YingK8/ESP32-BLE-Macro-Pad/macro-pad/src/departure_mono_upper_28.c

/*******************************************************************************
 * Size: 28 px
 * Bpp: 1
 * Opts: --bpp 1 --size 28 --stride 1 --align 1 --font DepartureMono-Regular.woff --symbols 1234567890:QWERTYUIOP[]\{}|ASDFGHJKL;':"ZXCVBNM,./>?<!@#$%^&*()_+-=  --format lvgl -o departure_mono_upper_28.c
 ******************************************************************************/

#ifdef __has_include
    #if __has_include("lvgl.h")
        #ifndef LV_LVGL_H_INCLUDE_SIMPLE
            #define LV_LVGL_H_INCLUDE_SIMPLE
        #endif
    #endif
#endif

#ifdef LV_LVGL_H_INCLUDE_SIMPLE
    #include "lvgl.h"
#else
    #include "lvgl/lvgl.h"
#endif



#ifndef DEPARTURE_MONO_UPPER_28
#define DEPARTURE_MONO_UPPER_28 1
#endif

#if DEPARTURE_MONO_UPPER_28

/*-----------------
 *    BITMAPS
 *----------------*/

/*Store the image of the glyphs*/
static LV_ATTRIBUTE_LARGE_CONST const uint8_t glyph_bitmap[] = {
    /* U+0020 " " */
    0x0,

    /* U+0021 "!" */
    0xff, 0xff, 0xff, 0xff, 0xff, 0xf8, 0x3, 0xf0,

    /* U+0022 "\"" */
    0xe7, 0xe7, 0xe7, 0xe7, 0xe7, 0xe7, 0xe7,

    /* U+0023 "#" */
    0x0, 0xc3, 0x0, 0x30, 0xc0, 0xc, 0x30, 0x3,
    0xc, 0x0, 0xc3, 0xf, 0xff, 0xf3, 0xff, 0xfc,
    0x1c, 0xf0, 0x7, 0x3c, 0x1, 0xcf, 0x0, 0x73,
    0xc0, 0x1c, 0xf0, 0x7, 0x3c, 0x3f, 0xff, 0xcf,
    0xff, 0xf0, 0xe3, 0x0, 0x38, 0xc0, 0xe, 0x30,
    0x3, 0x8c, 0x0, 0xe3, 0x0,

    /* U+0024 "$" */
    0x7, 0x0, 0x38, 0x1, 0xc0, 0x3f, 0x81, 0xfc,
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
    0x3, 0x80, 0x1c, 0x0, 0xe0, 0x7, 0x0, 0x0,
    0x0, 0x3e, 0x1, 0xf0, 0x70, 0x3, 0x80, 0x1c,
    0x0, 0xe0, 0x7, 0x0, 0x38, 0x1, 0xc0, 0xe,
    0x0, 0x70, 0x3, 0x83, 0xe0, 0x1f, 0x0
};


/*---------------------
 *  GLYPH DESCRIPTION
 *--------------------*/

static const lv_font_fmt_txt_glyph_dsc_t glyph_dsc[] = {
    {.bitmap_index = 0, .adv_w = 0, .box_w = 0, .box_h = 0, .ofs_x = 0, .ofs_y = 0} /* id = 0 reserved */,
    {.bitmap_index = 0, .adv_w = 285, .box_w = 1, .box_h = 1, .ofs_x = 0, .ofs_y = 0},
    {.bitmap_index = 1, .adv_w = 285, .box_w = 3, .box_h = 20, .ofs_x = 8, .ofs_y = 0},
    {.bitmap_index = 9, .adv_w = 285, .box_w = 8, .box_h = 7, .ofs_x = 5, .ofs_y = 13},
    {.bitmap_index = 16, .adv_w = 285, .box_w = 18, .box_h = 20, .ofs_x = 0, .ofs_y = 0},
    {.bitmap_index = 61, .adv_w = 285, .box_w = 13, .box_h = 25, .ofs_x = 3, .ofs_y = -2},
    {.bitmap_index = 102, .adv_w = 285, .box_w = 15, .box_h = 20, .ofs_x = 3, .ofs_y = 0},
    {.bitmap_index = 140, .adv_w = 285, .box_w = 15, .box_h = 20, .ofs_x = 3, .ofs_y = 0},
    {.bitmap_index = 178, .adv_w = 285, .box_w = 3, .box_h = 7, .ofs_x = 8, .ofs_y = 13},
    {.bitmap_index = 181, .adv_w = 285, .box_w = 9, .box_h = 24, .ofs_x = 5, .ofs_y = -2},
    {.bitmap_index = 208, .adv_w = 285, .box_w = 9, .box_h = 24, .ofs_x = 5, .ofs_y = -2},
    {.bitmap_index = 235, .adv_w = 285, .box_w = 13, .box_h = 12, .ofs_x = 3, .ofs_y = 8},
    {.bitmap_index = 255, .adv_w = 285, .box_w = 13, .box_h = 12, .ofs_x = 3, .ofs_y = 3},
    {.bitmap_index = 275, .adv_w = 285, .box_w = 5, .box_h = 7, .ofs_x = 5, .ofs_y = -2},
    {.bitmap_index = 280, .adv_w = 285, .box_w = 8, .box_h = 2, .ofs_x = 5, .ofs_y = 8},
    {.bitmap_index = 282, .adv_w = 285, .box_w = 3, .box_h = 5, .ofs_x = 8, .ofs_y = 0},
    {.bitmap_index = 284, .adv_w = 285, .box_w = 13, .box_h = 25, .ofs_x = 3, .ofs_y = -2},
    {.bitmap_index = 325, .adv_w = 285, .box_w = 13, .box_h = 20, .ofs_x = 3, .ofs_y = 0},
    {.bitmap_index = 358, .adv_w = 285, .box_w = 13, .box_h = 20, .ofs_x = 3, .ofs_y = 0},
    {.bitmap_index = 391, .adv_w = 285, .box_w = 13, .box_h = 20, .ofs_x = 3, .ofs_y = 0},
    {.bitmap_index = 424, .adv_w = 285, .box_w = 13, .box_h = 20, .ofs_x = 3, .ofs_y = 0},
    {.bitmap_index = 457, .adv_w = 285, .box_w = 13, .box_h = 20, .ofs_x = 3, .ofs_y = 0},
    {.bitmap_index = 490, .adv_w = 285, .box_w = 13, .box_h = 20, .ofs_x = 3, .ofs_y = 0},
    {.bitmap_index = 523, .adv_w = 285, .box_w = 13, .box_h = 20, .ofs_x = 3, .ofs_y = 0},
    {.bitmap_index = 556, .adv_w = 285, .box_w = 13, .box_h = 20, .ofs_x = 2, .ofs_y = 0},
    {.bitmap_index = 589, .adv_w = 285, .box_w = 13, .box_h = 20, .ofs_x = 3, .ofs_y = 0},
    {.bitmap_index = 622, .adv_w = 285, .box_w = 13, .box_h = 20, .ofs_x = 3, .ofs_y = 0},
    {.bitmap_index = 655, .adv_w = 285, .box_w = 3, .box_h = 15, .ofs_x = 8, .ofs_y = 0},
    {.bitmap_index = 661, .adv_w = 285, .box_w = 5, .box_h = 17, .ofs_x = 5, .ofs_y = -2},
    {.bitmap_index = 672, .adv_w = 285, .box_w = 10, .box_h = 17, .ofs_x = 3, .ofs_y = 0},
    {.bitmap_index = 694, .adv_w = 285, .box_w = 13, .box_h = 7, .ofs_x = 3, .ofs_y = 5},
    {.bitmap_index = 706, .adv_w = 285, .box_w = 10, .box_h = 17, .ofs_x = 5, .ofs_y = 0},
    {.bitmap_index = 728, .adv_w = 285, .box_w = 13, .box_h = 20, .ofs_x = 3, .ofs_y = 0},
    {.bitmap_index = 761, .adv_w = 285, .box_w = 13, .box_h = 20, .ofs_x = 3, .ofs_y = 0},
    {.bitmap_index = 794, .adv_w = 285, .box_w = 13, .box_h = 20, .ofs_x = 3, .ofs_y = 0},
    {.bitmap_index = 827, .adv_w = 285, .box_w = 13, .box_h = 20, .ofs_x = 3, .ofs_y = 0},
    {.bitmap_index = 860, .adv_w = 285, .box_w = 13, .box_h = 20, .ofs_x = 3, .ofs_y = 0},
    {.bitmap_index = 893, .adv_w = 285, .box_w = 13, .box_h = 20, .ofs_x = 3, .ofs_y = 0},
    {.bitmap_index = 926, .adv_w = 285, .box_w = 13, .box_h = 20, .ofs_x = 3, .ofs_y = 0},
    {.bitmap_index = 959, .adv_w = 285, .box_w = 13, .box_h = 20, .ofs_x = 3, .ofs_y = 0},
    {.bitmap_index = 992, .adv_w = 285, .box_w = 13, .box_h = 20, .ofs_x = 3, .ofs_y = 0},
    {.bitmap_index = 1025, .adv_w = 285, .box_w = 13, .box_h = 20, .ofs_x = 3, .ofs_y = 0},
    {.bitmap_index = 1058, .adv_w = 285, .box_w = 13, .box_h = 20, .ofs_x = 3, .ofs_y = 0},
    {.bitmap_index = 1091, .adv_w = 285, .box_w = 13, .box_h = 20, .ofs_x = 3, .ofs_y = 0},
    {.bitmap_index = 1124, .adv_w = 285, .box_w = 13, .box_h = 20, .ofs_x = 3, .ofs_y = 0},
    {.bitmap_index = 1157, .adv_w = 285, .box_w = 13, .box_h = 20, .ofs_x = 3, .ofs_y = 0},
    {.bitmap_index = 1190, .adv_w = 285, .box_w = 13, .box_h = 20, .ofs_x = 3, .ofs_y = 0},
    {.bitmap_index = 1223, .adv_w = 285, .box_w = 13, .box_h = 20, .ofs_x = 3, .ofs_y = 0},
    {.bitmap_index = 1256, .adv_w = 285, .box_w = 13, .box_h = 20, .ofs_x = 3, .ofs_y = 0},
    {.bitmap_index = 1289, .adv_w = 285, .box_w = 13, .box_h = 20, .ofs_x = 3, .ofs_y = 0},
    {.bitmap_index = 1322, .adv_w = 285, .box_w = 13, .box_h = 22, .ofs_x = 3, .ofs_y = -2},
    {.bitmap_index = 1358, .adv_w = 285, .box_w = 13, .box_h = 20, .ofs_x = 3, .ofs_y = 0},
    {.bitmap_index = 1391, .adv_w = 285, .box_w = 13, .box_h = 20, .ofs_x = 3, .ofs_y = 0},
    {.bitmap_index = 1424, .adv_w = 285, .box_w = 13, .box_h = 20, .ofs_x = 3, .ofs_y = 0},
    {.bitmap_index = 1457, .adv_w = 285, .box_w = 13, .box_h = 20, .ofs_x = 3, .ofs_y = 0},
    {.bitmap_index = 1490, .adv_w = 285, .box_w = 13, .box_h = 20, .ofs_x = 3, .ofs_y = 0},
    {.bitmap_index = 1523, .adv_w = 285, .box_w = 13, .box_h = 20, .ofs_x = 3, .ofs_y = 0},
    {.bitmap_index = 1556, .adv_w = 285, .box_w = 13, .box_h = 20, .ofs_x = 3, .ofs_y = 0},
    {.bitmap_index = 1589, .adv_w = 285, .box_w = 13, .box_h = 20, .ofs_x = 3, .ofs_y = 0},
    {.bitmap_index = 1622, .adv_w = 285, .box_w = 13, .box_h = 20, .ofs_x = 3, .ofs_y = 0},
    {.bitmap_index = 1655, .adv_w = 285, .box_w = 8, .box_h = 25, .ofs_x = 5, .ofs_y = -2},
    {.bitmap_index = 1680, .adv_w = 285, .box_w = 13, .box_h = 25, .ofs_x = 3, .ofs_y = -2},
    {.bitmap_index = 1721, .adv_w = 285, .box_w = 8, .box_h = 25, .ofs_x = 5, .ofs_y = -2},
    {.bitmap_index = 1746, .adv_w = 285, .box_w = 9, .box_h = 5, .ofs_x = 5, .ofs_y = 15},
    {.bitmap_index = 1752, .adv_w = 285, .box_w = 13, .box_h = 2, .ofs_x = 3, .ofs_y = 0},
    {.bitmap_index = 1756, .adv_w = 285, .box_w = 13, .box_h = 24, .ofs_x = 0, .ofs_y = -2},
    {.bitmap_index = 1795, .adv_w = 285, .box_w = 3, .box_h = 25, .ofs_x = 8, .ofs_y = -2},
    {.bitmap_index = 1805, .adv_w = 285, .box_w = 13, .box_h = 24, .ofs_x = 5, .ofs_y = -2}
};

/*---------------------
 *  CHARACTER MAPPING
 *--------------------*/



/*Collect the unicode lists and glyph_id offsets*/
static const lv_font_fmt_txt_cmap_t cmaps[] =
{
    {
        .range_start = 32, .range_length = 64, .glyph_id_start = 1,
        .unicode_list = NULL, .glyph_id_ofs_list = NULL, .list_length = 0, .type = LV_FONT_FMT_TXT_CMAP_FORMAT0_TINY
    },
    {
        .range_start = 123, .range_length = 3, .glyph_id_start = 65,
        .unicode_list = NULL, .glyph_id_ofs_list = NULL, .list_length = 0, .type = LV_FONT_FMT_TXT_CMAP_FORMAT0_TINY
    }
};



/*--------------------
 *  ALL CUSTOM DATA
 *--------------------*/

#if LVGL_VERSION_MAJOR == 8
/*Store all the custom data of the font*/
static  lv_font_fmt_txt_glyph_cache_t cache;
#endif

#if LVGL_VERSION_MAJOR >= 8
static const lv_font_fmt_txt_dsc_t font_dsc = {
#else
static lv_font_fmt_txt_dsc_t font_dsc = {
#endif
    .glyph_bitmap = glyph_bitmap,
    .glyph_dsc = glyph_dsc,
    .cmaps = cmaps,
    .kern_dsc = NULL,
    .kern_scale = 0,
    .cmap_num = 2,
    .bpp = 1,
    .kern_classes = 0,
    .bitmap_format = 0,
#if LVGL_VERSION_MAJOR == 8
    .cache = &cache
#endif

};



/*-----------------
 *  PUBLIC FONT
 *----------------*/

/*Initialize a public general font descriptor*/
#if LVGL_VERSION_MAJOR >= 8
const lv_font_t departure_mono_upper_28 = {
#else
lv_font_t departure_mono_upper_28 = {
#endif
    .get_glyph_dsc = lv_font_get_glyph_dsc_fmt_txt,    /*Function pointer to get glyph's data*/
    .get_glyph_bitmap = lv_font_get_bitmap_fmt_txt,    /*Function pointer to get glyph's bitmap*/
    .line_height = 25,          /*The maximum line height required by the font*/
    .base_line = 2,             /*Baseline measured from the bottom of the line*/
#if !(LVGL_VERSION_MAJOR == 6 && LVGL_VERSION_MINOR == 0)
    .subpx = LV_FONT_SUBPX_NONE,
#endif
#if LV_VERSION_CHECK(7, 4, 0) || LVGL_VERSION_MAJOR >= 8
    .underline_position = -3,
    .underline_thickness = 2,
#endif
    .dsc = &font_dsc,          /*The custom font data. Will be accessed by `get_glyph_bitmap/dsc` */
#if LV_VERSION_CHECK(8, 2, 0) || LVGL_VERSION_MAJOR >= 9
    .fallback = NULL,
#endif
    .user_data = NULL,
};



#endif /*#if DEPARTURE_MONO_UPPER_28*/
