YingK8/ESP32-BLE-Macro-Pad/macro-pad/src/departure_mono_upper_40.c

/*******************************************************************************
 * Size: 40 px
 * Bpp: 1
 * Opts: --bpp 1 --size 40 --no-compress --stride 1 --align 1 --font
 *DepartureMono-Regular.woff --symbols
 *1234567890:qwertyuiop[]\{}|asdfghjkl;':"zxcvbnm,./>?<!@#$%^&*()_+-=  --format
 *lvgl -o departure_mono_upper_40.c
 ******************************************************************************/

#ifdef __has_include
#if __has_include("lvgl.h")
#ifndef LV_LVGL_H_INCLUDE_SIMPLE
#define LV_LVGL_H_INCLUDE_SIMPLE
#endif
#endif
#endif

#ifdef LV_LVGL_H_INCLUDE_SIMPLE
#include "lvgl.h"
#else
#include "lvgl/lvgl.h"
#endif

#ifndef DEPARTURE_MONO_UPPER_40
#define DEPARTURE_MONO_UPPER_40 1
#endif

#if DEPARTURE_MONO_UPPER_40

/*-----------------
 *    BITMAPS
 *----------------*/

/*Store the image of the glyphs*/
static LV_ATTRIBUTE_LARGE_CONST const uint8_t glyph_bitmap[] = {
    /* U+0020 " " */
    0x0,

    /* U+0021 "!" */
    0xff, 0xff, 0xff, 0xff, 0xff, 0xff, 0xff, 0xff, 0xff, 0xff, 0xff, 0x0, 0x0,
    0xff, 0xf0,

    /* U+0022 "\"" */
    0xf1, 0xfe, 0x3f, 0xc7, 0xf8, 0xff, 0x1f, 0xe3, 0xfc, 0x7f, 0x8f, 0xf1,
    0xfe, 0x3f, 0xc7, 0x80,

    /* U+0023 "#" */
    0x0, 0x1e, 0x1e, 0x0, 0x7, 0x87, 0x80, 0x1, 0xe1, 0xe0, 0x0, 0x78, 0x78,
    0x0, 0x1e, 0x1e, 0x0, 0x7, 0x87, 0x80, 0x1, 0xe1, 0xe0, 0x7f, 0xff, 0xff,
    0x1f, 0xff, 0xff, 0xc7, 0xff, 0xff, 0xf1, 0xff, 0xff, 0xfc, 0x7, 0x87, 0x80,
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
     .adv_w = 407,
     .box_w = 4,
     .box_h = 36,
     .ofs_x = 11,
     .ofs_y = -4},
    {.bitmap_index = 3431,
     .adv_w = 407,
     .box_w = 18,
     .box_h = 36,
     .ofs_x = 7,
     .ofs_y = -3}};

/*---------------------
 *  CHARACTER MAPPING
 *--------------------*/

/*Collect the unicode lists and glyph_id offsets*/
static const lv_font_fmt_txt_cmap_t cmaps[] = {
    {.range_start = 32,
     .range_length = 33,
     .glyph_id_start = 1,
     .unicode_list = NULL,
     .glyph_id_ofs_list = NULL,
     .list_length = 0,
     .type = LV_FONT_FMT_TXT_CMAP_FORMAT0_TINY},
    {.range_start = 91,
     .range_length = 5,
     .glyph_id_start = 34,
     .unicode_list = NULL,
     .glyph_id_ofs_list = NULL,
     .list_length = 0,
     .type = LV_FONT_FMT_TXT_CMAP_FORMAT0_TINY},
    {.range_start = 97,
     .range_length = 29,
     .glyph_id_start = 39,
     .unicode_list = NULL,
     .glyph_id_ofs_list = NULL,
     .list_length = 0,
     .type = LV_FONT_FMT_TXT_CMAP_FORMAT0_TINY}};

/*--------------------
 *  ALL CUSTOM DATA
 *--------------------*/

#if LVGL_VERSION_MAJOR == 8
/*Store all the custom data of the font*/
static lv_font_fmt_txt_glyph_cache_t cache;
#endif

#if LVGL_VERSION_MAJOR >= 8
static const lv_font_fmt_txt_dsc_t font_dsc = {
#else
static lv_font_fmt_txt_dsc_t font_dsc = {
#endif
    .glyph_bitmap = glyph_bitmap,
    .glyph_dsc = glyph_dsc,
    .cmaps = cmaps,
    .kern_dsc = NULL,
    .kern_scale = 0,
    .cmap_num = 3,
    .bpp = 1,
    .kern_classes = 0,
    .bitmap_format = 0,
#if LVGL_VERSION_MAJOR == 8
    .cache = &cache
#endif

};

/*-----------------
 *  PUBLIC FONT
 *----------------*/

/*Initialize a public general font descriptor*/
#if LVGL_VERSION_MAJOR >= 8
const lv_font_t departure_mono_upper_40 = {
#else
lv_font_t departure_mono_upper_40 = {
#endif
    .get_glyph_dsc =
        lv_font_get_glyph_dsc_fmt_txt, /*Function pointer to get glyph's data*/
    .get_glyph_bitmap =
        lv_font_get_bitmap_fmt_txt, /*Function pointer to get glyph's bitmap*/
    .line_height = 40, /*The maximum line height required by the font*/
    .base_line = 7,    /*Baseline measured from the bottom of the line*/
#if !(LVGL_VERSION_MAJOR == 6 && LVGL_VERSION_MINOR == 0)
    .subpx = LV_FONT_SUBPX_NONE,
#endif
#if LV_VERSION_CHECK(7, 4, 0) || LVGL_VERSION_MAJOR >= 8
    .underline_position = -4,
    .underline_thickness = 2,
#endif

    .dsc = &font_dsc, /*The custom font data. Will be accessed by
                         `get_glyph_bitmap/dsc` */
#if LV_VERSION_CHECK(8, 2, 0) || LVGL_VERSION_MAJOR >= 9
    .fallback = NULL,
#endif
    .user_data = NULL,
};

#endif /*#if DEPARTURE_MONO_UPPER_40*/
