YingK8/ESP32-BLE-Macro-Pad/macro-pad/src/monogram_lower_40.c

/*******************************************************************************
 * Size: 40 px
 * Bpp: 1
 * Opts: --bpp 1 --size 40 --stride 1 --align 1 --font monogram-extended.ttf --symbols 1234567890:qwertyuiop[]\{}|asdfghjkl;':"zxcvbnm,./>?<!@#$%^&*()_+-=  --format lvgl -o monogram_lower_40.c
 ******************************************************************************/

#ifdef __has_include
    #if __has_include("lvgl.h")
        #ifndef LV_LVGL_H_INCLUDE_SIMPLE
            #define LV_LVGL_H_INCLUDE_SIMPLE
        #endif
    #endif
#endif

#ifdef LV_LVGL_H_INCLUDE_SIMPLE
    #include "lvgl.h"
#else
    #include "lvgl/lvgl.h"
#endif



#ifndef MONOGRAM_LOWER_40
#define MONOGRAM_LOWER_40 1
#endif

#if MONOGRAM_LOWER_40

/*-----------------
 *    BITMAPS
 *----------------*/

/*Store the image of the glyphs*/
static LV_ATTRIBUTE_LARGE_CONST const uint8_t glyph_bitmap[] = {
    /* U+0020 " " */
    0x0,

    /* U+0021 "!" */
    0xff, 0xff, 0xff, 0xff, 0xfe, 0x0, 0xfc,

    /* U+0022 "\"" */
    0xe7, 0xe7, 0xe7, 0xe7, 0xe7, 0xe7, 0xe7, 0xe7,

    /* U+0023 "#" */
    0x39, 0xc1, 0xce, 0x3f, 0xff, 0xff, 0xf3, 0x9c,
    0x1c, 0xe0, 0xe7, 0x7, 0x38, 0x39, 0xc1, 0xce,
    0x3f, 0xff, 0xff, 0xf3, 0x9c, 0x1c, 0xe0, 0xe7,
    0x0,

    /* U+0024 "$" */
    0x7, 0x0, 0x38, 0x1, 0xc0, 0x3f, 0xf1, 0xff,
    0xf3, 0x83, 0x9c, 0x4, 0xe0, 0x1f, 0xc0, 0xfe,
    0x1, 0xce, 0xe, 0x70, 0x70, 0x7f, 0xe3, 0xff,
    0x0, 0xe0, 0x7, 0x0, 0x38, 0x0,

    /* U+0025 "%" */
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

    /* U+007C "|" */
    0xff, 0xff, 0xff, 0xff, 0xff, 0xff, 0xfc,

    /* U+007D "}" */
    0xe0, 0x70, 0x6, 0x3, 0x1, 0x80, 0xc0, 0x60,
    0x0, 0x3, 0x81, 0xc6, 0x3, 0x1, 0x80, 0xc0,
    0x60, 0x0, 0xe0, 0x70, 0x0
};


/*---------------------
 *  GLYPH DESCRIPTION
 *--------------------*/

static const lv_font_fmt_txt_glyph_dsc_t glyph_dsc[] = {
    {.bitmap_index = 0, .adv_w = 0, .box_w = 0, .box_h = 0, .ofs_x = 0, .ofs_y = 0} /* id = 0 reserved */,
    {.bitmap_index = 0, .adv_w = 240, .box_w = 1, .box_h = 1, .ofs_x = 0, .ofs_y = 0},
    {.bitmap_index = 1, .adv_w = 240, .box_w = 3, .box_h = 18, .ofs_x = 5, .ofs_y = 0},
    {.bitmap_index = 8, .adv_w = 240, .box_w = 8, .box_h = 8, .ofs_x = 2, .ofs_y = 10},
    {.bitmap_index = 16, .adv_w = 240, .box_w = 13, .box_h = 15, .ofs_x = 0, .ofs_y = 0},
    {.bitmap_index = 41, .adv_w = 240, .box_w = 13, .box_h = 18, .ofs_x = 0, .ofs_y = 0},
    {.bitmap_index = 71, .adv_w = 240, .box_w = 13, .box_h = 18, .ofs_x = 0, .ofs_y = 0},
    {.bitmap_index = 101, .adv_w = 240, .box_w = 13, .box_h = 18, .ofs_x = 0, .ofs_y = 0},
    {.bitmap_index = 131, .adv_w = 240, .box_w = 3, .box_h = 8, .ofs_x = 5, .ofs_y = 10},
    {.bitmap_index = 134, .adv_w = 240, .box_w = 5, .box_h = 18, .ofs_x = 5, .ofs_y = 0},
    {.bitmap_index = 146, .adv_w = 240, .box_w = 5, .box_h = 18, .ofs_x = 2, .ofs_y = 0},
    {.bitmap_index = 158, .adv_w = 240, .box_w = 13, .box_h = 13, .ofs_x = 0, .ofs_y = 3},
    {.bitmap_index = 180, .adv_w = 240, .box_w = 13, .box_h = 13, .ofs_x = 0, .ofs_y = 3},
    {.bitmap_index = 202, .adv_w = 240, .box_w = 5, .box_h = 7, .ofs_x = 2, .ofs_y = -2},
    {.bitmap_index = 207, .adv_w = 240, .box_w = 13, .box_h = 2, .ofs_x = 0, .ofs_y = 8},
    {.bitmap_index = 211, .adv_w = 240, .box_w = 3, .box_h = 5, .ofs_x = 5, .ofs_y = 0},
    {.bitmap_index = 213, .adv_w = 240, .box_w = 13, .box_h = 18, .ofs_x = 0, .ofs_y = 0},
    {.bitmap_index = 243, .adv_w = 240, .box_w = 13, .box_h = 18, .ofs_x = 0, .ofs_y = 0},
    {.bitmap_index = 273, .adv_w = 240, .box_w = 13, .box_h = 18, .ofs_x = 0, .ofs_y = 0},
    {.bitmap_index = 303, .adv_w = 240, .box_w = 13, .box_h = 18, .ofs_x = 0, .ofs_y = 0},
    {.bitmap_index = 333, .adv_w = 240, .box_w = 13, .box_h = 18, .ofs_x = 0, .ofs_y = 0},
    {.bitmap_index = 363, .adv_w = 240, .box_w = 13, .box_h = 18, .ofs_x = 0, .ofs_y = 0},
    {.bitmap_index = 393, .adv_w = 240, .box_w = 13, .box_h = 18, .ofs_x = 0, .ofs_y = 0},
    {.bitmap_index = 423, .adv_w = 240, .box_w = 13, .box_h = 18, .ofs_x = 0, .ofs_y = 0},
    {.bitmap_index = 453, .adv_w = 240, .box_w = 13, .box_h = 18, .ofs_x = 0, .ofs_y = 0},
    {.bitmap_index = 483, .adv_w = 240, .box_w = 13, .box_h = 18, .ofs_x = 0, .ofs_y = 0},
    {.bitmap_index = 513, .adv_w = 240, .box_w = 13, .box_h = 18, .ofs_x = 0, .ofs_y = 0},
    {.bitmap_index = 543, .adv_w = 240, .box_w = 3, .box_h = 16, .ofs_x = 5, .ofs_y = 0},
    {.bitmap_index = 549, .adv_w = 240, .box_w = 5, .box_h = 18, .ofs_x = 2, .ofs_y = -2},
    {.bitmap_index = 561, .adv_w = 240, .box_w = 13, .box_h = 13, .ofs_x = 0, .ofs_y = 3},
    {.bitmap_index = 583, .adv_w = 240, .box_w = 13, .box_h = 7, .ofs_x = 0, .ofs_y = 6},
    {.bitmap_index = 595, .adv_w = 240, .box_w = 13, .box_h = 13, .ofs_x = 0, .ofs_y = 3},
    {.bitmap_index = 617, .adv_w = 240, .box_w = 13, .box_h = 18, .ofs_x = 0, .ofs_y = 0},
    {.bitmap_index = 647, .adv_w = 240, .box_w = 13, .box_h = 18, .ofs_x = 0, .ofs_y = 0},
    {.bitmap_index = 677, .adv_w = 240, .box_w = 5, .box_h = 18, .ofs_x = 5, .ofs_y = 0},
    {.bitmap_index = 689, .adv_w = 240, .box_w = 13, .box_h = 18, .ofs_x = 0, .ofs_y = 0},
    {.bitmap_index = 719, .adv_w = 240, .box_w = 6, .box_h = 18, .ofs_x = 2, .ofs_y = 0},
    {.bitmap_index = 733, .adv_w = 240, .box_w = 13, .box_h = 7, .ofs_x = 0, .ofs_y = 10},
    {.bitmap_index = 745, .adv_w = 240, .box_w = 13, .box_h = 2, .ofs_x = 0, .ofs_y = 0},
    {.bitmap_index = 749, .adv_w = 240, .box_w = 13, .box_h = 13, .ofs_x = 0, .ofs_y = 0},
    {.bitmap_index = 771, .adv_w = 240, .box_w = 13, .box_h = 18, .ofs_x = 0, .ofs_y = 0},
    {.bitmap_index = 801, .adv_w = 240, .box_w = 13, .box_h = 13, .ofs_x = 0, .ofs_y = 0},
    {.bitmap_index = 823, .adv_w = 240, .box_w = 13, .box_h = 18, .ofs_x = 0, .ofs_y = 0},
    {.bitmap_index = 853, .adv_w = 240, .box_w = 13, .box_h = 13, .ofs_x = 0, .ofs_y = 0},
    {.bitmap_index = 875, .adv_w = 240, .box_w = 13, .box_h = 18, .ofs_x = 0, .ofs_y = 0},
    {.bitmap_index = 905, .adv_w = 240, .box_w = 13, .box_h = 18, .ofs_x = 0, .ofs_y = -5},
    {.bitmap_index = 935, .adv_w = 240, .box_w = 13, .box_h = 18, .ofs_x = 0, .ofs_y = 0},
    {.bitmap_index = 965, .adv_w = 240, .box_w = 13, .box_h = 18, .ofs_x = 0, .ofs_y = 0},
    {.bitmap_index = 995, .adv_w = 240, .box_w = 13, .box_h = 23, .ofs_x = 0, .ofs_y = -5},
    {.bitmap_index = 1033, .adv_w = 240, .box_w = 13, .box_h = 18, .ofs_x = 0, .ofs_y = 0},
    {.bitmap_index = 1063, .adv_w = 240, .box_w = 13, .box_h = 18, .ofs_x = 0, .ofs_y = 0},
    {.bitmap_index = 1093, .adv_w = 240, .box_w = 13, .box_h = 13, .ofs_x = 0, .ofs_y = 0},
    {.bitmap_index = 1115, .adv_w = 240, .box_w = 13, .box_h = 13, .ofs_x = 0, .ofs_y = 0},
    {.bitmap_index = 1137, .adv_w = 240, .box_w = 13, .box_h = 13, .ofs_x = 0, .ofs_y = 0},
    {.bitmap_index = 1159, .adv_w = 240, .box_w = 13, .box_h = 18, .ofs_x = 0, .ofs_y = -5},
    {.bitmap_index = 1189, .adv_w = 240, .box_w = 13, .box_h = 18, .ofs_x = 0, .ofs_y = -5},
    {.bitmap_index = 1219, .adv_w = 240, .box_w = 13, .box_h = 13, .ofs_x = 0, .ofs_y = 0},
    {.bitmap_index = 1241, .adv_w = 240, .box_w = 13, .box_h = 13, .ofs_x = 0, .ofs_y = 0},
    {.bitmap_index = 1263, .adv_w = 240, .box_w = 13, .box_h = 18, .ofs_x = 0, .ofs_y = 0},
    {.bitmap_index = 1293, .adv_w = 240, .box_w = 13, .box_h = 13, .ofs_x = 0, .ofs_y = 0},
    {.bitmap_index = 1315, .adv_w = 240, .box_w = 13, .box_h = 13, .ofs_x = 0, .ofs_y = 0},
    {.bitmap_index = 1337, .adv_w = 240, .box_w = 13, .box_h = 13, .ofs_x = 0, .ofs_y = 0},
    {.bitmap_index = 1359, .adv_w = 240, .box_w = 13, .box_h = 13, .ofs_x = 0, .ofs_y = 0},
    {.bitmap_index = 1381, .adv_w = 240, .box_w = 13, .box_h = 18, .ofs_x = 0, .ofs_y = -5},
    {.bitmap_index = 1411, .adv_w = 240, .box_w = 13, .box_h = 13, .ofs_x = 0, .ofs_y = 0},
    {.bitmap_index = 1433, .adv_w = 240, .box_w = 9, .box_h = 18, .ofs_x = 2, .ofs_y = 0},
    {.bitmap_index = 1454, .adv_w = 240, .box_w = 3, .box_h = 18, .ofs_x = 5, .ofs_y = 0},
    {.bitmap_index = 1461, .adv_w = 240, .box_w = 9, .box_h = 18, .ofs_x = 2, .ofs_y = 0}
};

/*---------------------
 *  CHARACTER MAPPING
 *--------------------*/



/*Collect the unicode lists and glyph_id offsets*/
static const lv_font_fmt_txt_cmap_t cmaps[] =
{
    {
        .range_start = 32, .range_length = 33, .glyph_id_start = 1,
        .unicode_list = NULL, .glyph_id_ofs_list = NULL, .list_length = 0, .type = LV_FONT_FMT_TXT_CMAP_FORMAT0_TINY
    },
    {
        .range_start = 91, .range_length = 5, .glyph_id_start = 34,
        .unicode_list = NULL, .glyph_id_ofs_list = NULL, .list_length = 0, .type = LV_FONT_FMT_TXT_CMAP_FORMAT0_TINY
    },
    {
        .range_start = 97, .range_length = 29, .glyph_id_start = 39,
        .unicode_list = NULL, .glyph_id_ofs_list = NULL, .list_length = 0, .type = LV_FONT_FMT_TXT_CMAP_FORMAT0_TINY
    }
};



/*--------------------
 *  ALL CUSTOM DATA
 *--------------------*/

#if LVGL_VERSION_MAJOR == 8
/*Store all the custom data of the font*/
static  lv_font_fmt_txt_glyph_cache_t cache;
#endif

#if LVGL_VERSION_MAJOR >= 8
static const lv_font_fmt_txt_dsc_t font_dsc = {
#else
static lv_font_fmt_txt_dsc_t font_dsc = {
#endif
    .glyph_bitmap = glyph_bitmap,
    .glyph_dsc = glyph_dsc,
    .cmaps = cmaps,
    .kern_dsc = NULL,
    .kern_scale = 0,
    .cmap_num = 3,
    .bpp = 1,
    .kern_classes = 0,
    .bitmap_format = 0,
#if LVGL_VERSION_MAJOR == 8
    .cache = &cache
#endif

};



/*-----------------
 *  PUBLIC FONT
 *----------------*/

/*Initialize a public general font descriptor*/
#if LVGL_VERSION_MAJOR >= 8
const lv_font_t monogram_lower_40 = {
#else
lv_font_t monogram_lower_40 = {
#endif
    .get_glyph_dsc = lv_font_get_glyph_dsc_fmt_txt,    /*Function pointer to get glyph's data*/
    .get_glyph_bitmap = lv_font_get_bitmap_fmt_txt,    /*Function pointer to get glyph's bitmap*/
    .line_height = 23,          /*The maximum line height required by the font*/
    .base_line = 5,             /*Baseline measured from the bottom of the line*/
#if !(LVGL_VERSION_MAJOR == 6 && LVGL_VERSION_MINOR == 0)
    .subpx = LV_FONT_SUBPX_NONE,
#endif
#if LV_VERSION_CHECK(7, 4, 0) || LVGL_VERSION_MAJOR >= 8
    .underline_position = -5,
    .underline_thickness = 2,
#endif
    .dsc = &font_dsc,          /*The custom font data. Will be accessed by `get_glyph_bitmap/dsc` */
#if LV_VERSION_CHECK(8, 2, 0) || LVGL_VERSION_MAJOR >= 9
    .fallback = NULL,
#endif
    .user_data = NULL,
};



#endif /*#if MONOGRAM_LOWER_40*/
