YingK8/ESP32-BLE-Macro-Pad/macro-pad/src/monogram_lower_counter_125.c

/*******************************************************************************
 * Size: 125 px
 * Bpp: 1
 * Opts: --bpp 1 --size 125 --no-compress --stride 1 --align 1 --font monogram-extended.ttf --symbols 1234567890: --format lvgl -o monogram_lower_counter_125.c
 ******************************************************************************/

#ifdef __has_include
    #if __has_include("lvgl.h")
        #ifndef LV_LVGL_H_INCLUDE_SIMPLE
            #define LV_LVGL_H_INCLUDE_SIMPLE
        #endif
    #endif
#endif

#ifdef LV_LVGL_H_INCLUDE_SIMPLE
    #include "lvgl.h"
#else
    #include "lvgl/lvgl.h"
#endif



#ifndef MONOGRAM_LOWER_COUNTER_125
#define MONOGRAM_LOWER_COUNTER_125 1
#endif

#if MONOGRAM_LOWER_COUNTER_125

/*-----------------
 *    BITMAPS
 *----------------*/

/*Store the image of the glyphs*/
static LV_ATTRIBUTE_LARGE_CONST const uint8_t glyph_bitmap[] = {
    /* U+0030 "0" */
    0x0, 0xff, 0xff, 0xfe, 0x0, 0x1, 0xff, 0xff,
    0xfc, 0x0, 0x3, 0xff, 0xff, 0xf8, 0x0, 0x7,
    0xff, 0xff, 0xf0, 0x0, 0xf, 0xff, 0xff, 0xe0,
    0x0, 0x1f, 0xff, 0xff, 0xc0, 0x0, 0x3f, 0xff,
    0xff, 0x80, 0x0, 0x7f, 0xff, 0xff, 0x0, 0xff,
    0x0, 0x0, 0x1, 0xff, 0xfe, 0x0, 0x0, 0x3,
    0xff, 0xfc, 0x0, 0x0, 0x7, 0xff, 0xf8, 0x0,
    0x0, 0xf, 0xff, 0xf0, 0x0, 0x0, 0x1f, 0xff,
    0xe0, 0x0, 0x0, 0x3f, 0xff, 0xc0, 0x0, 0x0,
    0x7f, 0xff, 0x80, 0x0, 0x0, 0xff, 0xff, 0x0,
    0x0, 0xff, 0xff, 0xfe, 0x0, 0x1, 0xff, 0xff,
    0xfc, 0x0, 0x3, 0xff, 0xff, 0xf8, 0x0, 0x7,
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
    0x0, 0x0, 0x0, 0x0, 0x0, 0x0, 0x0, 0x0,
    0x0, 0x0, 0x0, 0x0, 0x0, 0x0, 0x0, 0x0,
    0xff, 0xff, 0xff, 0xff, 0xff, 0xff, 0xff, 0xff,
    0xff, 0xff, 0xff, 0xff, 0xff, 0xff, 0xff
};


/*---------------------
 *  GLYPH DESCRIPTION
 *--------------------*/

static const lv_font_fmt_txt_glyph_dsc_t glyph_dsc[] = {
    {.bitmap_index = 0, .adv_w = 0, .box_w = 0, .box_h = 0, .ofs_x = 0, .ofs_y = 0} /* id = 0 reserved */,
    {.bitmap_index = 0, .adv_w = 750, .box_w = 39, .box_h = 55, .ofs_x = 0, .ofs_y = 0},
    {.bitmap_index = 269, .adv_w = 750, .box_w = 39, .box_h = 55, .ofs_x = 0, .ofs_y = 0},
    {.bitmap_index = 538, .adv_w = 750, .box_w = 39, .box_h = 55, .ofs_x = 0, .ofs_y = 0},
    {.bitmap_index = 807, .adv_w = 750, .box_w = 39, .box_h = 55, .ofs_x = 0, .ofs_y = 0},
    {.bitmap_index = 1076, .adv_w = 750, .box_w = 39, .box_h = 55, .ofs_x = 0, .ofs_y = 0},
    {.bitmap_index = 1345, .adv_w = 750, .box_w = 39, .box_h = 55, .ofs_x = 0, .ofs_y = 0},
    {.bitmap_index = 1614, .adv_w = 750, .box_w = 39, .box_h = 55, .ofs_x = 0, .ofs_y = 0},
    {.bitmap_index = 1883, .adv_w = 750, .box_w = 40, .box_h = 55, .ofs_x = 0, .ofs_y = 0},
    {.bitmap_index = 2158, .adv_w = 750, .box_w = 39, .box_h = 55, .ofs_x = 0, .ofs_y = 0},
    {.bitmap_index = 2427, .adv_w = 750, .box_w = 39, .box_h = 55, .ofs_x = 0, .ofs_y = 0},
    {.bitmap_index = 2696, .adv_w = 750, .box_w = 8, .box_h = 47, .ofs_x = 16, .ofs_y = 0}
};

/*---------------------
 *  CHARACTER MAPPING
 *--------------------*/



/*Collect the unicode lists and glyph_id offsets*/
static const lv_font_fmt_txt_cmap_t cmaps[] =
{
    {
        .range_start = 48, .range_length = 11, .glyph_id_start = 1,
        .unicode_list = NULL, .glyph_id_ofs_list = NULL, .list_length = 0, .type = LV_FONT_FMT_TXT_CMAP_FORMAT0_TINY
    }
};



/*--------------------
 *  ALL CUSTOM DATA
 *--------------------*/

#if LVGL_VERSION_MAJOR == 8
/*Store all the custom data of the font*/
static  lv_font_fmt_txt_glyph_cache_t cache;
#endif

#if LVGL_VERSION_MAJOR >= 8
static const lv_font_fmt_txt_dsc_t font_dsc = {
#else
static lv_font_fmt_txt_dsc_t font_dsc = {
#endif
    .glyph_bitmap = glyph_bitmap,
    .glyph_dsc = glyph_dsc,
    .cmaps = cmaps,
    .kern_dsc = NULL,
    .kern_scale = 0,
    .cmap_num = 1,
    .bpp = 1,
    .kern_classes = 0,
    .bitmap_format = 0,
#if LVGL_VERSION_MAJOR == 8
    .cache = &cache
#endif

};



/*-----------------
 *  PUBLIC FONT
 *----------------*/

/*Initialize a public general font descriptor*/
#if LVGL_VERSION_MAJOR >= 8
const lv_font_t monogram_lower_counter_125 = {
#else
lv_font_t monogram_lower_counter_125 = {
#endif
    .get_glyph_dsc = lv_font_get_glyph_dsc_fmt_txt,    /*Function pointer to get glyph's data*/
    .get_glyph_bitmap = lv_font_get_bitmap_fmt_txt,    /*Function pointer to get glyph's bitmap*/
    .line_height = 55,          /*The maximum line height required by the font*/
    .base_line = 0,             /*Baseline measured from the bottom of the line*/
#if !(LVGL_VERSION_MAJOR == 6 && LVGL_VERSION_MINOR == 0)
    .subpx = LV_FONT_SUBPX_NONE,
#endif
#if LV_VERSION_CHECK(7, 4, 0) || LVGL_VERSION_MAJOR >= 8
    .underline_position = -16,
    .underline_thickness = 6,
#endif
    .dsc = &font_dsc,          /*The custom font data. Will be accessed by `get_glyph_bitmap/dsc` */
#if LV_VERSION_CHECK(8, 2, 0) || LVGL_VERSION_MAJOR >= 9
    .fallback = NULL,
#endif
    .user_data = NULL,
};



#endif /*#if MONOGRAM_LOWER_COUNTER_125*/
