YingK8/ESP32-BLE-Macro-Pad/macro-pad/src/dots_28.c

/*******************************************************************************
 * Size: 28 px
 * Bpp: 1
 * Opts: --bpp 1 --size 28 --stride 1 --align 1 --font LED Dot-Matrix.ttf --symbols QWERTYUIOPASDFGHJKLZXCVBNM0!:.-123456789?%=+  --format lvgl -o dots_28.c
 ******************************************************************************/

#ifdef __has_include
    #if __has_include("lvgl.h")
        #ifndef LV_LVGL_H_INCLUDE_SIMPLE
            #define LV_LVGL_H_INCLUDE_SIMPLE
        #endif
    #endif
#endif

#ifdef LV_LVGL_H_INCLUDE_SIMPLE
    #include "lvgl.h"
#else
    #include "lvgl/lvgl.h"
#endif



#ifndef DOTS_28
#define DOTS_28 1
#endif

#if DOTS_28

/*-----------------
 *    BITMAPS
 *----------------*/

/*Store the image of the glyphs*/
static LV_ATTRIBUTE_LARGE_CONST const uint8_t glyph_bitmap[] = {
    /* U+0020 " " */
    0x0,

    /* U+0021 "!" */
    0xf3, 0xcf, 0x3c, 0xf0, 0xf,

    /* U+0025 "%" */
    0xd8, 0xf, 0x60, 0x30, 0x0, 0x36, 0x3, 0xd8,
    0xc, 0x0, 0x0, 0x6, 0x0, 0x18, 0x0, 0x0,
    0xc, 0x0, 0x30, 0x0, 0x0, 0x18, 0x0, 0x60,
    0x0, 0x0, 0x30, 0x1b, 0xc0, 0x6c, 0x0, 0xc,
    0x6, 0xf0, 0x1b,

    /* U+002B "+" */
    0x0, 0x0, 0xc, 0x0, 0x30, 0x0, 0x80, 0x3,
    0x0, 0xc, 0xc, 0xb4, 0xb6, 0xdf, 0xda, 0x48,
    0xc, 0x0, 0x30, 0x0, 0x80, 0x3, 0x0, 0xc,
    0x0, 0x20, 0x0,

    /* U+002D "-" */
    0xdb, 0x6f, 0x6d, 0xb0,

    /* U+0030 "0" */
    0x1b, 0x60, 0x6d, 0x80, 0x0, 0x30, 0x3, 0xc0,
    0xc, 0x0, 0xc, 0x6, 0xf0, 0x1b, 0x0, 0x3,
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
    0x0, 0x0, 0x0, 0xc0, 0x3, 0x0, 0x0, 0x0,
    0x30, 0x0, 0xc0,

    /* U+0055 "U" */
    0xc0, 0xf, 0x0, 0x30, 0x0, 0x30, 0x3, 0xc0,
    0xc, 0x0, 0xc, 0x0, 0xf0, 0x3, 0x0, 0x3,
    0x0, 0x3c, 0x0, 0xc0, 0x0, 0xc0, 0xf, 0x0,
    0x30, 0x0, 0x30, 0x3, 0xc0, 0xc, 0x0, 0x1,
    0xb6, 0x6, 0xd8,

    /* U+0056 "V" */
    0xc0, 0xf, 0x0, 0x30, 0x0, 0x30, 0x3, 0xc0,
    0xc, 0x0, 0xc, 0x0, 0xf0, 0x3, 0x0, 0x3,
    0x0, 0x3c, 0x0, 0xc0, 0x0, 0xc0, 0xf, 0x0,
    0x30, 0x0, 0x6, 0x18, 0x18, 0x60, 0x0, 0x0,
    0x30, 0x0, 0xc0,

    /* U+0057 "W" */
    0xc0, 0xf, 0x0, 0x30, 0x0, 0x30, 0x3, 0xc0,
    0xc, 0x0, 0xc, 0x0, 0xf0, 0x3, 0x0, 0x3,
    0xc, 0x3c, 0x30, 0xc0, 0x0, 0xc3, 0xf, 0xc,
    0x30, 0x0, 0x36, 0x1b, 0xd8, 0x6c, 0x0, 0xc,
    0x0, 0xf0, 0x3,

    /* U+0058 "X" */
    0xc0, 0xf, 0x0, 0x30, 0x0, 0x30, 0x3, 0xc0,
    0xc, 0x0, 0x1, 0x86, 0x6, 0x18, 0x0, 0x0,
    0xc, 0x0, 0x30, 0x0, 0x0, 0x18, 0x60, 0x61,
    0x80, 0x0, 0x30, 0x3, 0xc0, 0xc, 0x0, 0xc,
    0x0, 0xf0, 0x3,

    /* U+0059 "Y" */
    0xc0, 0xf, 0x0, 0x30, 0x0, 0x30, 0x3, 0xc0,
    0xc, 0x0, 0xc, 0x0, 0xf0, 0x3, 0x0, 0x0,
    0x61, 0x81, 0x86, 0x0, 0x0, 0x3, 0x0, 0xc,
    0x0, 0x0, 0x0, 0xc0, 0x3, 0x0, 0x0, 0x0,
    0x30, 0x0, 0xc0,

    /* U+005A "Z" */
    0xdb, 0x6f, 0x6d, 0xb0, 0x0, 0x0, 0x3, 0x0,
    0xc, 0x0, 0x0, 0x6, 0x0, 0x18, 0x0, 0x0,
    0xc, 0x0, 0x30, 0x0, 0x0, 0x18, 0x0, 0x60,
    0x0, 0x0, 0x30, 0x0, 0xc0, 0x0, 0x0, 0xd,
    0xb6, 0xf6, 0xdb
};


/*---------------------
 *  GLYPH DESCRIPTION
 *--------------------*/

static const lv_font_fmt_txt_glyph_dsc_t glyph_dsc[] = {
    {.bitmap_index = 0, .adv_w = 0, .box_w = 0, .box_h = 0, .ofs_x = 0, .ofs_y = 0} /* id = 0 reserved */,
    {.bitmap_index = 0, .adv_w = 196, .box_w = 1, .box_h = 1, .ofs_x = 0, .ofs_y = 0},
    {.bitmap_index = 1, .adv_w = 101, .box_w = 2, .box_h = 20, .ofs_x = 2, .ofs_y = 0},
    {.bitmap_index = 6, .adv_w = 289, .box_w = 14, .box_h = 20, .ofs_x = 2, .ofs_y = 0},
    {.bitmap_index = 41, .adv_w = 284, .box_w = 14, .box_h = 15, .ofs_x = 2, .ofs_y = 3},
    {.bitmap_index = 68, .adv_w = 284, .box_w = 14, .box_h = 2, .ofs_x = 2, .ofs_y = 9},
    {.bitmap_index = 72, .adv_w = 289, .box_w = 14, .box_h = 20, .ofs_x = 2, .ofs_y = 0},
    {.bitmap_index = 107, .adv_w = 195, .box_w = 8, .box_h = 20, .ofs_x = 2, .ofs_y = 0},
    {.bitmap_index = 127, .adv_w = 289, .box_w = 14, .box_h = 20, .ofs_x = 2, .ofs_y = 0},
    {.bitmap_index = 162, .adv_w = 289, .box_w = 14, .box_h = 20, .ofs_x = 2, .ofs_y = 0},
    {.bitmap_index = 197, .adv_w = 289, .box_w = 14, .box_h = 20, .ofs_x = 2, .ofs_y = 0},
    {.bitmap_index = 232, .adv_w = 289, .box_w = 14, .box_h = 20, .ofs_x = 2, .ofs_y = 0},
    {.bitmap_index = 267, .adv_w = 289, .box_w = 14, .box_h = 20, .ofs_x = 2, .ofs_y = 0},
    {.bitmap_index = 302, .adv_w = 289, .box_w = 14, .box_h = 20, .ofs_x = 2, .ofs_y = 0},
    {.bitmap_index = 337, .adv_w = 289, .box_w = 14, .box_h = 20, .ofs_x = 2, .ofs_y = 0},
    {.bitmap_index = 372, .adv_w = 289, .box_w = 14, .box_h = 20, .ofs_x = 2, .ofs_y = 0},
    {.bitmap_index = 407, .adv_w = 284, .box_w = 14, .box_h = 6, .ofs_x = 2, .ofs_y = 7},
    {.bitmap_index = 418, .adv_w = 289, .box_w = 14, .box_h = 20, .ofs_x = 2, .ofs_y = 0},
    {.bitmap_index = 453, .adv_w = 289, .box_w = 14, .box_h = 20, .ofs_x = 2, .ofs_y = 0},
    {.bitmap_index = 488, .adv_w = 289, .box_w = 14, .box_h = 20, .ofs_x = 2, .ofs_y = 0},
    {.bitmap_index = 523, .adv_w = 289, .box_w = 14, .box_h = 20, .ofs_x = 2, .ofs_y = 0},
    {.bitmap_index = 558, .adv_w = 289, .box_w = 14, .box_h = 20, .ofs_x = 2, .ofs_y = 0},
    {.bitmap_index = 593, .adv_w = 289, .box_w = 14, .box_h = 20, .ofs_x = 2, .ofs_y = 0},
    {.bitmap_index = 628, .adv_w = 289, .box_w = 14, .box_h = 20, .ofs_x = 2, .ofs_y = 0},
    {.bitmap_index = 663, .adv_w = 289, .box_w = 14, .box_h = 20, .ofs_x = 2, .ofs_y = 0},
    {.bitmap_index = 698, .adv_w = 289, .box_w = 14, .box_h = 20, .ofs_x = 2, .ofs_y = 0},
    {.bitmap_index = 733, .adv_w = 195, .box_w = 8, .box_h = 20, .ofs_x = 2, .ofs_y = 0},
    {.bitmap_index = 753, .adv_w = 289, .box_w = 14, .box_h = 20, .ofs_x = 2, .ofs_y = 0},
    {.bitmap_index = 788, .adv_w = 289, .box_w = 14, .box_h = 20, .ofs_x = 2, .ofs_y = 0},
    {.bitmap_index = 823, .adv_w = 289, .box_w = 14, .box_h = 20, .ofs_x = 2, .ofs_y = 0},
    {.bitmap_index = 858, .adv_w = 289, .box_w = 14, .box_h = 20, .ofs_x = 2, .ofs_y = 0},
    {.bitmap_index = 893, .adv_w = 289, .box_w = 14, .box_h = 20, .ofs_x = 2, .ofs_y = 0},
    {.bitmap_index = 928, .adv_w = 289, .box_w = 14, .box_h = 20, .ofs_x = 2, .ofs_y = 0},
    {.bitmap_index = 963, .adv_w = 289, .box_w = 14, .box_h = 20, .ofs_x = 2, .ofs_y = 0},
    {.bitmap_index = 998, .adv_w = 289, .box_w = 14, .box_h = 20, .ofs_x = 2, .ofs_y = 0},
    {.bitmap_index = 1033, .adv_w = 289, .box_w = 14, .box_h = 20, .ofs_x = 2, .ofs_y = 0},
    {.bitmap_index = 1068, .adv_w = 289, .box_w = 14, .box_h = 20, .ofs_x = 2, .ofs_y = 0},
    {.bitmap_index = 1103, .adv_w = 289, .box_w = 14, .box_h = 20, .ofs_x = 2, .ofs_y = 0},
    {.bitmap_index = 1138, .adv_w = 289, .box_w = 14, .box_h = 20, .ofs_x = 2, .ofs_y = 0},
    {.bitmap_index = 1173, .adv_w = 289, .box_w = 14, .box_h = 20, .ofs_x = 2, .ofs_y = 0},
    {.bitmap_index = 1208, .adv_w = 289, .box_w = 14, .box_h = 20, .ofs_x = 2, .ofs_y = 0},
    {.bitmap_index = 1243, .adv_w = 289, .box_w = 14, .box_h = 20, .ofs_x = 2, .ofs_y = 0},
    {.bitmap_index = 1278, .adv_w = 289, .box_w = 14, .box_h = 20, .ofs_x = 2, .ofs_y = 0},
    {.bitmap_index = 1313, .adv_w = 289, .box_w = 14, .box_h = 20, .ofs_x = 2, .ofs_y = 0}
};

/*---------------------
 *  CHARACTER MAPPING
 *--------------------*/

static const uint8_t glyph_id_ofs_list_0[] = {
    0, 1, 0, 0, 0, 2, 0, 0,
    0, 0, 0, 3, 0, 4, 0, 0,
    5, 6, 7, 8, 9, 10, 11, 12,
    13, 14, 0, 0, 0, 15, 0, 16
};

/*Collect the unicode lists and glyph_id offsets*/
static const lv_font_fmt_txt_cmap_t cmaps[] =
{
    {
        .range_start = 32, .range_length = 32, .glyph_id_start = 1,
        .unicode_list = NULL, .glyph_id_ofs_list = glyph_id_ofs_list_0, .list_length = 32, .type = LV_FONT_FMT_TXT_CMAP_FORMAT0_FULL
    },
    {
        .range_start = 65, .range_length = 26, .glyph_id_start = 18,
        .unicode_list = NULL, .glyph_id_ofs_list = NULL, .list_length = 0, .type = LV_FONT_FMT_TXT_CMAP_FORMAT0_TINY
    }
};



/*--------------------
 *  ALL CUSTOM DATA
 *--------------------*/

#if LVGL_VERSION_MAJOR == 8
/*Store all the custom data of the font*/
static  lv_font_fmt_txt_glyph_cache_t cache;
#endif

#if LVGL_VERSION_MAJOR >= 8
static const lv_font_fmt_txt_dsc_t font_dsc = {
#else
static lv_font_fmt_txt_dsc_t font_dsc = {
#endif
    .glyph_bitmap = glyph_bitmap,
    .glyph_dsc = glyph_dsc,
    .cmaps = cmaps,
    .kern_dsc = NULL,
    .kern_scale = 0,
    .cmap_num = 2,
    .bpp = 1,
    .kern_classes = 0,
    .bitmap_format = 0,
#if LVGL_VERSION_MAJOR == 8
    .cache = &cache
#endif

};



/*-----------------
 *  PUBLIC FONT
 *----------------*/

/*Initialize a public general font descriptor*/
#if LVGL_VERSION_MAJOR >= 8
const lv_font_t dots_28 = {
#else
lv_font_t dots_28 = {
#endif
    .get_glyph_dsc = lv_font_get_glyph_dsc_fmt_txt,    /*Function pointer to get glyph's data*/
    .get_glyph_bitmap = lv_font_get_bitmap_fmt_txt,    /*Function pointer to get glyph's bitmap*/
    .line_height = 20,          /*The maximum line height required by the font*/
    .base_line = 0,             /*Baseline measured from the bottom of the line*/
#if !(LVGL_VERSION_MAJOR == 6 && LVGL_VERSION_MINOR == 0)
    .subpx = LV_FONT_SUBPX_NONE,
#endif
#if LV_VERSION_CHECK(7, 4, 0) || LVGL_VERSION_MAJOR >= 8
    .underline_position = -9,
    .underline_thickness = 1,
#endif
    .dsc = &font_dsc,          /*The custom font data. Will be accessed by `get_glyph_bitmap/dsc` */
#if LV_VERSION_CHECK(8, 2, 0) || LVGL_VERSION_MAJOR >= 9
    .fallback = NULL,
#endif
    .user_data = NULL,
};



#endif /*#if DOTS_28*/
