YingK8/ESP32-BLE-Macro-Pad/macro-pad/src/dots_32.c

/*******************************************************************************
 * Size: 32 px
 * Bpp: 1
 * Opts: --bpp 1 --size 32 --stride 1 --align 1 --font LED Dot-Matrix.ttf --symbols QWERTYUIOPASDFGHJKLZXCVBNM0!:.-123456789?%=+  --format lvgl -o dots_32.c
 ******************************************************************************/

#ifdef __has_include
    #if __has_include("lvgl.h")
        #ifndef LV_LVGL_H_INCLUDE_SIMPLE
            #define LV_LVGL_H_INCLUDE_SIMPLE
        #endif
    #endif
#endif

#ifdef LV_LVGL_H_INCLUDE_SIMPLE
    #include "lvgl.h"
#else
    #include "lvgl/lvgl.h"
#endif



#ifndef DOTS_32
#define DOTS_32 1
#endif

#if DOTS_32

/*-----------------
 *    BITMAPS
 *----------------*/

/*Store the image of the glyphs*/
static LV_ATTRIBUTE_LARGE_CONST const uint8_t glyph_bitmap[] = {
    /* U+0020 " " */
    0x0,

    /* U+0021 "!" */
    0xff, 0xff, 0xc7, 0xff, 0xff, 0xff, 0x0, 0xf,
    0xf8,

    /* U+0025 "%" */
    0xfc, 0x7, 0xfc, 0x7, 0xfc, 0x7, 0xfc, 0x7,
    0xfc, 0x7, 0xfc, 0x7, 0x0, 0x0, 0x0, 0x38,
    0x0, 0x38, 0x0, 0x38, 0x1, 0xc0, 0x1, 0xc0,
    0x1, 0xc0, 0x1c, 0x0, 0x1c, 0x0, 0x1c, 0x0,
    0x0, 0x0, 0xe0, 0x3f, 0xe0, 0x3f, 0xe0, 0x3f,
    0xe0, 0x3f, 0xe0, 0x3f, 0xe0, 0x3f,

    /* U+002B "+" */
    0x1, 0x80, 0x1, 0xc0, 0x0, 0x80, 0x1, 0x80,
    0x1, 0xc0, 0x1, 0x80, 0x0, 0x0, 0xed, 0xbf,
    0xed, 0xbf, 0x0, 0x0, 0x1, 0x80, 0x1, 0xc0,
    0x1, 0x80, 0x1, 0x80, 0x1, 0xc0, 0x1, 0x80,

    /* U+002D "-" */
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
    0xe0, 0x7, 0xe0, 0x7, 0xe0, 0x7, 0xe0, 0x7,
    0xe0, 0x7, 0xe0, 0x7, 0x0, 0x0, 0xe0, 0x7,
    0xe0, 0x7, 0xe0, 0x7, 0xe0, 0x7, 0xe0, 0x7,
    0xe0, 0x7, 0xe0, 0x7, 0xe0, 0x7, 0xe0, 0x7,
    0x0, 0x0, 0x1c, 0x38, 0x1c, 0x38, 0x1c, 0x38,
    0x1, 0xc0, 0x1, 0xc0, 0x1, 0xc0,

    /* U+0057 "W" */
    0xe0, 0x7, 0xe0, 0x7, 0xe0, 0x7, 0xe0, 0x7,
    0xe0, 0x7, 0xe0, 0x7, 0x0, 0x0, 0xe0, 0x7,
    0xe0, 0x7, 0xe0, 0x7, 0xe1, 0xc7, 0xe1, 0xc7,
    0xe1, 0xc7, 0xe1, 0xc7, 0xe1, 0xc7, 0xe1, 0xc7,
    0x0, 0x0, 0xfc, 0x3f, 0xfc, 0x3f, 0xfc, 0x3f,
    0xe0, 0x7, 0xe0, 0x7, 0xe0, 0x7,

    /* U+0058 "X" */
    0xe0, 0x7, 0xe0, 0x7, 0xe0, 0x7, 0xe0, 0x7,
    0xe0, 0x7, 0xe0, 0x7, 0x0, 0x0, 0x1c, 0x38,
    0x1c, 0x38, 0x1c, 0x38, 0x1, 0xc0, 0x1, 0xc0,
    0x1, 0xc0, 0x1c, 0x38, 0x1c, 0x38, 0x1c, 0x38,
    0x0, 0x0, 0xe0, 0x7, 0xe0, 0x7, 0xe0, 0x7,
    0xe0, 0x7, 0xe0, 0x7, 0xe0, 0x7,

    /* U+0059 "Y" */
    0xe0, 0x7, 0xe0, 0x7, 0xe0, 0x7, 0xe0, 0x7,
    0xe0, 0x7, 0xe0, 0x7, 0x0, 0x0, 0xe0, 0x7,
    0xe0, 0x7, 0xe0, 0x7, 0x1c, 0x38, 0x1c, 0x38,
    0x1c, 0x38, 0x1, 0xc0, 0x1, 0xc0, 0x1, 0xc0,
    0x0, 0x0, 0x1, 0xc0, 0x1, 0xc0, 0x1, 0xc0,
    0x1, 0xc0, 0x1, 0xc0, 0x1, 0xc0,

    /* U+005A "Z" */
    0xfd, 0xff, 0xfd, 0xff, 0xfd, 0xff, 0x0, 0x7,
    0x0, 0x7, 0x0, 0x7, 0x0, 0x0, 0x0, 0x38,
    0x0, 0x38, 0x0, 0x38, 0x1, 0xc0, 0x1, 0xc0,
    0x1, 0xc0, 0x1c, 0x0, 0x1c, 0x0, 0x1c, 0x0,
    0x0, 0x0, 0xe0, 0x0, 0xe0, 0x0, 0xe0, 0x0,
    0xfd, 0xff, 0xfd, 0xff, 0xfd, 0xff
};


/*---------------------
 *  GLYPH DESCRIPTION
 *--------------------*/

static const lv_font_fmt_txt_glyph_dsc_t glyph_dsc[] = {
    {.bitmap_index = 0, .adv_w = 0, .box_w = 0, .box_h = 0, .ofs_x = 0, .ofs_y = 0} /* id = 0 reserved */,
    {.bitmap_index = 0, .adv_w = 224, .box_w = 1, .box_h = 1, .ofs_x = 0, .ofs_y = 0},
    {.bitmap_index = 1, .adv_w = 116, .box_w = 3, .box_h = 23, .ofs_x = 2, .ofs_y = 0},
    {.bitmap_index = 10, .adv_w = 330, .box_w = 16, .box_h = 23, .ofs_x = 2, .ofs_y = 0},
    {.bitmap_index = 56, .adv_w = 325, .box_w = 16, .box_h = 16, .ofs_x = 2, .ofs_y = 4},
    {.bitmap_index = 88, .adv_w = 325, .box_w = 16, .box_h = 3, .ofs_x = 2, .ofs_y = 11},
    {.bitmap_index = 94, .adv_w = 330, .box_w = 16, .box_h = 23, .ofs_x = 2, .ofs_y = 0},
    {.bitmap_index = 140, .adv_w = 223, .box_w = 9, .box_h = 23, .ofs_x = 2, .ofs_y = 0},
    {.bitmap_index = 166, .adv_w = 330, .box_w = 16, .box_h = 23, .ofs_x = 2, .ofs_y = 0},
    {.bitmap_index = 212, .adv_w = 330, .box_w = 16, .box_h = 23, .ofs_x = 2, .ofs_y = 0},
    {.bitmap_index = 258, .adv_w = 330, .box_w = 16, .box_h = 23, .ofs_x = 2, .ofs_y = 0},
    {.bitmap_index = 304, .adv_w = 330, .box_w = 16, .box_h = 23, .ofs_x = 2, .ofs_y = 0},
    {.bitmap_index = 350, .adv_w = 330, .box_w = 16, .box_h = 23, .ofs_x = 2, .ofs_y = 0},
    {.bitmap_index = 396, .adv_w = 330, .box_w = 16, .box_h = 23, .ofs_x = 2, .ofs_y = 0},
    {.bitmap_index = 442, .adv_w = 330, .box_w = 16, .box_h = 23, .ofs_x = 2, .ofs_y = 0},
    {.bitmap_index = 488, .adv_w = 330, .box_w = 16, .box_h = 23, .ofs_x = 2, .ofs_y = 0},
    {.bitmap_index = 534, .adv_w = 325, .box_w = 16, .box_h = 8, .ofs_x = 2, .ofs_y = 8},
    {.bitmap_index = 550, .adv_w = 330, .box_w = 16, .box_h = 23, .ofs_x = 2, .ofs_y = 0},
    {.bitmap_index = 596, .adv_w = 330, .box_w = 17, .box_h = 23, .ofs_x = 2, .ofs_y = 0},
    {.bitmap_index = 645, .adv_w = 330, .box_w = 16, .box_h = 23, .ofs_x = 2, .ofs_y = 0},
    {.bitmap_index = 691, .adv_w = 330, .box_w = 16, .box_h = 23, .ofs_x = 2, .ofs_y = 0},
    {.bitmap_index = 737, .adv_w = 330, .box_w = 16, .box_h = 23, .ofs_x = 2, .ofs_y = 0},
    {.bitmap_index = 783, .adv_w = 330, .box_w = 16, .box_h = 23, .ofs_x = 2, .ofs_y = 0},
    {.bitmap_index = 829, .adv_w = 330, .box_w = 16, .box_h = 23, .ofs_x = 2, .ofs_y = 0},
    {.bitmap_index = 875, .adv_w = 330, .box_w = 16, .box_h = 23, .ofs_x = 2, .ofs_y = 0},
    {.bitmap_index = 921, .adv_w = 330, .box_w = 16, .box_h = 23, .ofs_x = 2, .ofs_y = 0},
    {.bitmap_index = 967, .adv_w = 223, .box_w = 9, .box_h = 23, .ofs_x = 2, .ofs_y = 0},
    {.bitmap_index = 993, .adv_w = 330, .box_w = 16, .box_h = 23, .ofs_x = 2, .ofs_y = 0},
    {.bitmap_index = 1039, .adv_w = 330, .box_w = 16, .box_h = 23, .ofs_x = 2, .ofs_y = 0},
    {.bitmap_index = 1085, .adv_w = 330, .box_w = 16, .box_h = 23, .ofs_x = 2, .ofs_y = 0},
    {.bitmap_index = 1131, .adv_w = 330, .box_w = 16, .box_h = 23, .ofs_x = 2, .ofs_y = 0},
    {.bitmap_index = 1177, .adv_w = 330, .box_w = 16, .box_h = 23, .ofs_x = 2, .ofs_y = 0},
    {.bitmap_index = 1223, .adv_w = 330, .box_w = 16, .box_h = 23, .ofs_x = 2, .ofs_y = 0},
    {.bitmap_index = 1269, .adv_w = 330, .box_w = 16, .box_h = 23, .ofs_x = 2, .ofs_y = 0},
    {.bitmap_index = 1315, .adv_w = 330, .box_w = 16, .box_h = 23, .ofs_x = 2, .ofs_y = 0},
    {.bitmap_index = 1361, .adv_w = 330, .box_w = 16, .box_h = 23, .ofs_x = 2, .ofs_y = 0},
    {.bitmap_index = 1407, .adv_w = 330, .box_w = 16, .box_h = 23, .ofs_x = 2, .ofs_y = 0},
    {.bitmap_index = 1453, .adv_w = 330, .box_w = 16, .box_h = 23, .ofs_x = 2, .ofs_y = 0},
    {.bitmap_index = 1499, .adv_w = 330, .box_w = 16, .box_h = 23, .ofs_x = 2, .ofs_y = 0},
    {.bitmap_index = 1545, .adv_w = 330, .box_w = 16, .box_h = 23, .ofs_x = 2, .ofs_y = 0},
    {.bitmap_index = 1591, .adv_w = 330, .box_w = 16, .box_h = 23, .ofs_x = 2, .ofs_y = 0},
    {.bitmap_index = 1637, .adv_w = 330, .box_w = 16, .box_h = 23, .ofs_x = 2, .ofs_y = 0},
    {.bitmap_index = 1683, .adv_w = 330, .box_w = 16, .box_h = 23, .ofs_x = 2, .ofs_y = 0},
    {.bitmap_index = 1729, .adv_w = 330, .box_w = 16, .box_h = 23, .ofs_x = 2, .ofs_y = 0}
};

/*---------------------
 *  CHARACTER MAPPING
 *--------------------*/

static const uint8_t glyph_id_ofs_list_0[] = {
    0, 1, 0, 0, 0, 2, 0, 0,
    0, 0, 0, 3, 0, 4, 0, 0,
    5, 6, 7, 8, 9, 10, 11, 12,
    13, 14, 0, 0, 0, 15, 0, 16
};

/*Collect the unicode lists and glyph_id offsets*/
static const lv_font_fmt_txt_cmap_t cmaps[] =
{
    {
        .range_start = 32, .range_length = 32, .glyph_id_start = 1,
        .unicode_list = NULL, .glyph_id_ofs_list = glyph_id_ofs_list_0, .list_length = 32, .type = LV_FONT_FMT_TXT_CMAP_FORMAT0_FULL
    },
    {
        .range_start = 65, .range_length = 26, .glyph_id_start = 18,
        .unicode_list = NULL, .glyph_id_ofs_list = NULL, .list_length = 0, .type = LV_FONT_FMT_TXT_CMAP_FORMAT0_TINY
    }
};



/*--------------------
 *  ALL CUSTOM DATA
 *--------------------*/

#if LVGL_VERSION_MAJOR == 8
/*Store all the custom data of the font*/
static  lv_font_fmt_txt_glyph_cache_t cache;
#endif

#if LVGL_VERSION_MAJOR >= 8
static const lv_font_fmt_txt_dsc_t font_dsc = {
#else
static lv_font_fmt_txt_dsc_t font_dsc = {
#endif
    .glyph_bitmap = glyph_bitmap,
    .glyph_dsc = glyph_dsc,
    .cmaps = cmaps,
    .kern_dsc = NULL,
    .kern_scale = 0,
    .cmap_num = 2,
    .bpp = 1,
    .kern_classes = 0,
    .bitmap_format = 0,
#if LVGL_VERSION_MAJOR == 8
    .cache = &cache
#endif

};



/*-----------------
 *  PUBLIC FONT
 *----------------*/

/*Initialize a public general font descriptor*/
#if LVGL_VERSION_MAJOR >= 8
const lv_font_t dots_32 = {
#else
lv_font_t dots_32 = {
#endif
    .get_glyph_dsc = lv_font_get_glyph_dsc_fmt_txt,    /*Function pointer to get glyph's data*/
    .get_glyph_bitmap = lv_font_get_bitmap_fmt_txt,    /*Function pointer to get glyph's bitmap*/
    .line_height = 23,          /*The maximum line height required by the font*/
    .base_line = 0,             /*Baseline measured from the bottom of the line*/
#if !(LVGL_VERSION_MAJOR == 6 && LVGL_VERSION_MINOR == 0)
    .subpx = LV_FONT_SUBPX_NONE,
#endif
#if LV_VERSION_CHECK(7, 4, 0) || LVGL_VERSION_MAJOR >= 8
    .underline_position = -10,
    .underline_thickness = 2,
#endif
    .dsc = &font_dsc,          /*The custom font data. Will be accessed by `get_glyph_bitmap/dsc` */
#if LV_VERSION_CHECK(8, 2, 0) || LVGL_VERSION_MAJOR >= 9
    .fallback = NULL,
#endif
    .user_data = NULL,
};



#endif /*#if DOTS_32*/
