YingK8/ESP32-BLE-Macro-Pad/macro-pad/src/monogram_lower_32.c

/*******************************************************************************
 * Size: 32 px
 * Bpp: 1
 * Opts: --bpp 1 --size 32 --stride 1 --align 1 --font monogram-extended.ttf --symbols 1234567890:qwertyuiop[]\{}|asdfghjkl;':"zxcvbnm,./>?<!@#$%^&*()_+-=  --format lvgl -o monogram_lower_32.c
 ******************************************************************************/

#ifdef __has_include
    #if __has_include("lvgl.h")
        #ifndef LV_LVGL_H_INCLUDE_SIMPLE
            #define LV_LVGL_H_INCLUDE_SIMPLE
        #endif
    #endif
#endif

#ifdef LV_LVGL_H_INCLUDE_SIMPLE
    #include "lvgl.h"
#else
    #include "lvgl/lvgl.h"
#endif



#ifndef MONOGRAM_LOWER_32
#define MONOGRAM_LOWER_32 1
#endif

#if MONOGRAM_LOWER_32

/*-----------------
 *    BITMAPS
 *----------------*/

/*Store the image of the glyphs*/
static LV_ATTRIBUTE_LARGE_CONST const uint8_t glyph_bitmap[] = {
    /* U+0020 " " */
    0x0,

    /* U+0021 "!" */
    0xff, 0xff, 0xf0, 0xf0,

    /* U+0022 "\"" */
    0xcf, 0x3c, 0xf3, 0xcf, 0x30,

    /* U+0023 "#" */
    0x33, 0xc, 0xcf, 0xff, 0xff, 0x33, 0xc, 0xc3,
    0x30, 0xcc, 0xff, 0xff, 0xf3, 0x30, 0xcc,

    /* U+0024 "$" */
    0xc, 0x3, 0x3, 0xfc, 0xff, 0xcc, 0x33, 0x3,
    0xf0, 0xfc, 0xc, 0xc3, 0x3f, 0xf3, 0xfc, 0xc,
    0x3, 0x0,

    /* U+0025 "%" */
    0xc0, 0xf0, 0x3c, 0xf, 0x3, 0x3, 0x0, 0xc0,
    0xc0, 0x30, 0x30, 0xc, 0xc, 0xf, 0x3, 0xc0,
    0xf0, 0x30,

    /* U+0026 "&" */
    0x3c, 0xf, 0xc, 0x33, 0xc, 0xc3, 0x30, 0xc3,
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
    0xc, 0x33, 0xc, 0x30, 0xcc, 0x30, 0x30, 0xc3,
    0xc, 0xc, 0x30,

    /* U+007C "|" */
    0xff, 0xff, 0xff, 0xf0,

    /* U+007D "}" */
    0xc3, 0x3, 0xc, 0x30, 0xc0, 0xc3, 0x30, 0xc3,
    0xc, 0xc3, 0x0
};


/*---------------------
 *  GLYPH DESCRIPTION
 *--------------------*/

static const lv_font_fmt_txt_glyph_dsc_t glyph_dsc[] = {
    {.bitmap_index = 0, .adv_w = 0, .box_w = 0, .box_h = 0, .ofs_x = 0, .ofs_y = 0} /* id = 0 reserved */,
    {.bitmap_index = 0, .adv_w = 192, .box_w = 1, .box_h = 1, .ofs_x = 0, .ofs_y = 0},
    {.bitmap_index = 1, .adv_w = 192, .box_w = 2, .box_h = 14, .ofs_x = 4, .ofs_y = 0},
    {.bitmap_index = 5, .adv_w = 192, .box_w = 6, .box_h = 6, .ofs_x = 2, .ofs_y = 8},
    {.bitmap_index = 10, .adv_w = 192, .box_w = 10, .box_h = 12, .ofs_x = 0, .ofs_y = 0},
    {.bitmap_index = 25, .adv_w = 192, .box_w = 10, .box_h = 14, .ofs_x = 0, .ofs_y = 0},
    {.bitmap_index = 43, .adv_w = 192, .box_w = 10, .box_h = 14, .ofs_x = 0, .ofs_y = 0},
    {.bitmap_index = 61, .adv_w = 192, .box_w = 10, .box_h = 14, .ofs_x = 0, .ofs_y = 0},
    {.bitmap_index = 79, .adv_w = 192, .box_w = 2, .box_h = 6, .ofs_x = 4, .ofs_y = 8},
    {.bitmap_index = 81, .adv_w = 192, .box_w = 4, .box_h = 14, .ofs_x = 4, .ofs_y = 0},
    {.bitmap_index = 88, .adv_w = 192, .box_w = 4, .box_h = 14, .ofs_x = 2, .ofs_y = 0},
    {.bitmap_index = 95, .adv_w = 192, .box_w = 10, .box_h = 10, .ofs_x = 0, .ofs_y = 2},
    {.bitmap_index = 108, .adv_w = 192, .box_w = 10, .box_h = 10, .ofs_x = 0, .ofs_y = 2},
    {.bitmap_index = 121, .adv_w = 192, .box_w = 4, .box_h = 6, .ofs_x = 2, .ofs_y = -2},
    {.bitmap_index = 124, .adv_w = 192, .box_w = 10, .box_h = 2, .ofs_x = 0, .ofs_y = 6},
    {.bitmap_index = 127, .adv_w = 192, .box_w = 2, .box_h = 4, .ofs_x = 4, .ofs_y = 0},
    {.bitmap_index = 128, .adv_w = 192, .box_w = 10, .box_h = 14, .ofs_x = 0, .ofs_y = 0},
    {.bitmap_index = 146, .adv_w = 192, .box_w = 10, .box_h = 14, .ofs_x = 0, .ofs_y = 0},
    {.bitmap_index = 164, .adv_w = 192, .box_w = 10, .box_h = 14, .ofs_x = 0, .ofs_y = 0},
    {.bitmap_index = 182, .adv_w = 192, .box_w = 10, .box_h = 14, .ofs_x = 0, .ofs_y = 0},
    {.bitmap_index = 200, .adv_w = 192, .box_w = 10, .box_h = 14, .ofs_x = 0, .ofs_y = 0},
    {.bitmap_index = 218, .adv_w = 192, .box_w = 10, .box_h = 14, .ofs_x = 0, .ofs_y = 0},
    {.bitmap_index = 236, .adv_w = 192, .box_w = 10, .box_h = 14, .ofs_x = 0, .ofs_y = 0},
    {.bitmap_index = 254, .adv_w = 192, .box_w = 10, .box_h = 14, .ofs_x = 0, .ofs_y = 0},
    {.bitmap_index = 272, .adv_w = 192, .box_w = 10, .box_h = 14, .ofs_x = 0, .ofs_y = 0},
    {.bitmap_index = 290, .adv_w = 192, .box_w = 10, .box_h = 14, .ofs_x = 0, .ofs_y = 0},
    {.bitmap_index = 308, .adv_w = 192, .box_w = 10, .box_h = 14, .ofs_x = 0, .ofs_y = 0},
    {.bitmap_index = 326, .adv_w = 192, .box_w = 2, .box_h = 12, .ofs_x = 4, .ofs_y = 0},
    {.bitmap_index = 329, .adv_w = 192, .box_w = 4, .box_h = 14, .ofs_x = 2, .ofs_y = -2},
    {.bitmap_index = 336, .adv_w = 192, .box_w = 10, .box_h = 10, .ofs_x = 0, .ofs_y = 2},
    {.bitmap_index = 349, .adv_w = 192, .box_w = 10, .box_h = 6, .ofs_x = 0, .ofs_y = 4},
    {.bitmap_index = 357, .adv_w = 192, .box_w = 10, .box_h = 10, .ofs_x = 0, .ofs_y = 2},
    {.bitmap_index = 370, .adv_w = 192, .box_w = 10, .box_h = 14, .ofs_x = 0, .ofs_y = 0},
    {.bitmap_index = 388, .adv_w = 192, .box_w = 10, .box_h = 14, .ofs_x = 0, .ofs_y = 0},
    {.bitmap_index = 406, .adv_w = 192, .box_w = 4, .box_h = 14, .ofs_x = 4, .ofs_y = 0},
    {.bitmap_index = 413, .adv_w = 192, .box_w = 10, .box_h = 14, .ofs_x = 0, .ofs_y = 0},
    {.bitmap_index = 431, .adv_w = 192, .box_w = 4, .box_h = 14, .ofs_x = 2, .ofs_y = 0},
    {.bitmap_index = 438, .adv_w = 192, .box_w = 10, .box_h = 6, .ofs_x = 0, .ofs_y = 8},
    {.bitmap_index = 446, .adv_w = 192, .box_w = 10, .box_h = 2, .ofs_x = 0, .ofs_y = 0},
    {.bitmap_index = 449, .adv_w = 192, .box_w = 10, .box_h = 10, .ofs_x = 0, .ofs_y = 0},
    {.bitmap_index = 462, .adv_w = 192, .box_w = 10, .box_h = 14, .ofs_x = 0, .ofs_y = 0},
    {.bitmap_index = 480, .adv_w = 192, .box_w = 10, .box_h = 10, .ofs_x = 0, .ofs_y = 0},
    {.bitmap_index = 493, .adv_w = 192, .box_w = 10, .box_h = 14, .ofs_x = 0, .ofs_y = 0},
    {.bitmap_index = 511, .adv_w = 192, .box_w = 10, .box_h = 10, .ofs_x = 0, .ofs_y = 0},
    {.bitmap_index = 524, .adv_w = 192, .box_w = 10, .box_h = 14, .ofs_x = 0, .ofs_y = 0},
    {.bitmap_index = 542, .adv_w = 192, .box_w = 10, .box_h = 14, .ofs_x = 0, .ofs_y = -4},
    {.bitmap_index = 560, .adv_w = 192, .box_w = 10, .box_h = 14, .ofs_x = 0, .ofs_y = 0},
    {.bitmap_index = 578, .adv_w = 192, .box_w = 10, .box_h = 14, .ofs_x = 0, .ofs_y = 0},
    {.bitmap_index = 596, .adv_w = 192, .box_w = 10, .box_h = 18, .ofs_x = 0, .ofs_y = -4},
    {.bitmap_index = 619, .adv_w = 192, .box_w = 10, .box_h = 14, .ofs_x = 0, .ofs_y = 0},
    {.bitmap_index = 637, .adv_w = 192, .box_w = 10, .box_h = 14, .ofs_x = 0, .ofs_y = 0},
    {.bitmap_index = 655, .adv_w = 192, .box_w = 10, .box_h = 10, .ofs_x = 0, .ofs_y = 0},
    {.bitmap_index = 668, .adv_w = 192, .box_w = 10, .box_h = 10, .ofs_x = 0, .ofs_y = 0},
    {.bitmap_index = 681, .adv_w = 192, .box_w = 10, .box_h = 10, .ofs_x = 0, .ofs_y = 0},
    {.bitmap_index = 694, .adv_w = 192, .box_w = 10, .box_h = 14, .ofs_x = 0, .ofs_y = -4},
    {.bitmap_index = 712, .adv_w = 192, .box_w = 10, .box_h = 14, .ofs_x = 0, .ofs_y = -4},
    {.bitmap_index = 730, .adv_w = 192, .box_w = 10, .box_h = 10, .ofs_x = 0, .ofs_y = 0},
    {.bitmap_index = 743, .adv_w = 192, .box_w = 10, .box_h = 10, .ofs_x = 0, .ofs_y = 0},
    {.bitmap_index = 756, .adv_w = 192, .box_w = 10, .box_h = 14, .ofs_x = 0, .ofs_y = 0},
    {.bitmap_index = 774, .adv_w = 192, .box_w = 10, .box_h = 10, .ofs_x = 0, .ofs_y = 0},
    {.bitmap_index = 787, .adv_w = 192, .box_w = 10, .box_h = 10, .ofs_x = 0, .ofs_y = 0},
    {.bitmap_index = 800, .adv_w = 192, .box_w = 10, .box_h = 10, .ofs_x = 0, .ofs_y = 0},
    {.bitmap_index = 813, .adv_w = 192, .box_w = 10, .box_h = 10, .ofs_x = 0, .ofs_y = 0},
    {.bitmap_index = 826, .adv_w = 192, .box_w = 10, .box_h = 14, .ofs_x = 0, .ofs_y = -4},
    {.bitmap_index = 844, .adv_w = 192, .box_w = 10, .box_h = 10, .ofs_x = 0, .ofs_y = 0},
    {.bitmap_index = 857, .adv_w = 192, .box_w = 6, .box_h = 14, .ofs_x = 2, .ofs_y = 0},
    {.bitmap_index = 868, .adv_w = 192, .box_w = 2, .box_h = 14, .ofs_x = 4, .ofs_y = 0},
    {.bitmap_index = 872, .adv_w = 192, .box_w = 6, .box_h = 14, .ofs_x = 2, .ofs_y = 0}
};

/*---------------------
 *  CHARACTER MAPPING
 *--------------------*/



/*Collect the unicode lists and glyph_id offsets*/
static const lv_font_fmt_txt_cmap_t cmaps[] =
{
    {
        .range_start = 32, .range_length = 33, .glyph_id_start = 1,
        .unicode_list = NULL, .glyph_id_ofs_list = NULL, .list_length = 0, .type = LV_FONT_FMT_TXT_CMAP_FORMAT0_TINY
    },
    {
        .range_start = 91, .range_length = 5, .glyph_id_start = 34,
        .unicode_list = NULL, .glyph_id_ofs_list = NULL, .list_length = 0, .type = LV_FONT_FMT_TXT_CMAP_FORMAT0_TINY
    },
    {
        .range_start = 97, .range_length = 29, .glyph_id_start = 39,
        .unicode_list = NULL, .glyph_id_ofs_list = NULL, .list_length = 0, .type = LV_FONT_FMT_TXT_CMAP_FORMAT0_TINY
    }
};



/*--------------------
 *  ALL CUSTOM DATA
 *--------------------*/

#if LVGL_VERSION_MAJOR == 8
/*Store all the custom data of the font*/
static  lv_font_fmt_txt_glyph_cache_t cache;
#endif

#if LVGL_VERSION_MAJOR >= 8
static const lv_font_fmt_txt_dsc_t font_dsc = {
#else
static lv_font_fmt_txt_dsc_t font_dsc = {
#endif
    .glyph_bitmap = glyph_bitmap,
    .glyph_dsc = glyph_dsc,
    .cmaps = cmaps,
    .kern_dsc = NULL,
    .kern_scale = 0,
    .cmap_num = 3,
    .bpp = 1,
    .kern_classes = 0,
    .bitmap_format = 0,
#if LVGL_VERSION_MAJOR == 8
    .cache = &cache
#endif

};



/*-----------------
 *  PUBLIC FONT
 *----------------*/

/*Initialize a public general font descriptor*/
#if LVGL_VERSION_MAJOR >= 8
const lv_font_t monogram_lower_32 = {
#else
lv_font_t monogram_lower_32 = {
#endif
    .get_glyph_dsc = lv_font_get_glyph_dsc_fmt_txt,    /*Function pointer to get glyph's data*/
    .get_glyph_bitmap = lv_font_get_bitmap_fmt_txt,    /*Function pointer to get glyph's bitmap*/
    .line_height = 18,          /*The maximum line height required by the font*/
    .base_line = 4,             /*Baseline measured from the bottom of the line*/
#if !(LVGL_VERSION_MAJOR == 6 && LVGL_VERSION_MINOR == 0)
    .subpx = LV_FONT_SUBPX_NONE,
#endif
#if LV_VERSION_CHECK(7, 4, 0) || LVGL_VERSION_MAJOR >= 8
    .underline_position = -4,
    .underline_thickness = 2,
#endif
    .dsc = &font_dsc,          /*The custom font data. Will be accessed by `get_glyph_bitmap/dsc` */
#if LV_VERSION_CHECK(8, 2, 0) || LVGL_VERSION_MAJOR >= 9
    .fallback = NULL,
#endif
    .user_data = NULL,
};



#endif /*#if MONOGRAM_LOWER_32*/
