YingK8/ESP32-BLE-Macro-Pad/macro-pad/src/monogram_lower_numbers_72.c

/*******************************************************************************
 * Size: 72 px
 * Bpp: 1
 * Opts: --bpp 1 --size 72 --stride 1 --align 1 --font monogram-extended.ttf --symbols 1234567890: --format lvgl -o monogram_lower_numbers_72.c
 ******************************************************************************/

#ifdef __has_include
    #if __has_include("lvgl.h")
        #ifndef LV_LVGL_H_INCLUDE_SIMPLE
            #define LV_LVGL_H_INCLUDE_SIMPLE
        #endif
    #endif
#endif

#ifdef LV_LVGL_H_INCLUDE_SIMPLE
    #include "lvgl.h"
#else
    #include "lvgl/lvgl.h"
#endif



#ifndef MONOGRAM_LOWER_NUMBERS_72
#define MONOGRAM_LOWER_NUMBERS_72 1
#endif

#if MONOGRAM_LOWER_NUMBERS_72

/*-----------------
 *    BITMAPS
 *----------------*/

/*Store the image of the glyphs*/
static LV_ATTRIBUTE_LARGE_CONST const uint8_t glyph_bitmap[] = {
    /* U+0030 "0" */
    0x7, 0xff, 0xc0, 0xf, 0xff, 0x80, 0x1f, 0xff,
    0x0, 0x3f, 0xfe, 0xf, 0x80, 0x3, 0xff, 0x0,
    0x7, 0xfe, 0x0, 0xf, 0xfc, 0x0, 0x1f, 0xf8,
    0x0, 0x3f, 0xf0, 0x7, 0xff, 0xe0, 0xf, 0xff,
    0xc0, 0x1f, 0xff, 0x80, 0x3f, 0xff, 0x0, 0x87,
    0xfe, 0x1f, 0xf, 0xfc, 0x3e, 0x1f, 0xf8, 0x7c,
    0x3f, 0xf0, 0xf8, 0x7f, 0xfe, 0x0, 0xff, 0xfc,
    0x1, 0xff, 0xf8, 0x3, 0xff, 0xf0, 0x7, 0xfe,
    0x0, 0xf, 0xfc, 0x0, 0x1f, 0xf8, 0x0, 0x3f,
    0xf0, 0x0, 0x7f, 0xe0, 0x0, 0xf8, 0x0, 0x0,
    0x0, 0x7f, 0xfc, 0x0, 0xff, 0xf8, 0x1, 0xff,
    0xf0, 0x3, 0xff, 0xe0,

    /* U+0031 "1" */
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
    0xc0, 0x0, 0x7, 0x80, 0x1, 0xf0, 0x0, 0x3,
    0xe0, 0x0, 0x7, 0xc0, 0x0, 0xf, 0x80, 0x0,
    0x1f, 0x0, 0x0, 0x3e, 0x0, 0x0, 0x7c, 0x0,
    0x0, 0xf8, 0x0, 0x1, 0xf0, 0x0, 0x3, 0xe0,
    0x0, 0x7, 0xc0, 0x0, 0xf, 0x80, 0x0, 0x1f,
    0x0, 0x0, 0x3e, 0x0,

    /* U+0038 "8" */
    0x7, 0xff, 0xc0, 0xf, 0xff, 0x80, 0x1f, 0xff,
    0x0, 0x3f, 0xfe, 0xf, 0x80, 0x3, 0xff, 0x0,
    0x7, 0xfe, 0x0, 0xf, 0xfc, 0x0, 0x1f, 0xf8,
    0x0, 0x3f, 0xf0, 0x0, 0x7f, 0xe0, 0x0, 0xff,
    0xc0, 0x1, 0xff, 0x80, 0x3, 0xe0, 0x0, 0x0,
    0x1, 0xff, 0xf0, 0x3, 0xff, 0xe0, 0x7, 0xff,
    0xc0, 0xf, 0xff, 0x83, 0xe0, 0x0, 0xff, 0xc0,
    0x1, 0xff, 0x80, 0x3, 0xff, 0x0, 0x7, 0xfe,
    0x0, 0xf, 0xfc, 0x0, 0x1f, 0xf8, 0x0, 0x3f,
    0xf0, 0x0, 0x7f, 0xe0, 0x0, 0xf8, 0x0, 0x0,
    0x0, 0x7f, 0xfc, 0x0, 0xff, 0xf8, 0x1, 0xff,
    0xf0, 0x3, 0xff, 0xe0,

    /* U+0039 "9" */
    0x7, 0xff, 0xc0, 0xf, 0xff, 0x80, 0x1f, 0xff,
    0x0, 0x3f, 0xfe, 0xf, 0x80, 0x3, 0xff, 0x0,
    0x7, 0xfe, 0x0, 0xf, 0xfc, 0x0, 0x1f, 0xf8,
    0x0, 0x3f, 0xf0, 0x0, 0x7f, 0xe0, 0x0, 0xff,
    0xc0, 0x1, 0xff, 0x80, 0x3, 0xe0, 0x0, 0x7,
    0xc1, 0xff, 0xff, 0x83, 0xff, 0xff, 0x7, 0xff,
    0xfe, 0xf, 0xff, 0xfc, 0x0, 0x0, 0xf8, 0x0,
    0x1, 0xf0, 0x0, 0x3, 0xe0, 0x0, 0x7, 0xc0,
    0x0, 0xf, 0xfc, 0x0, 0x1f, 0xf8, 0x0, 0x3f,
    0xf0, 0x0, 0x7f, 0xe0, 0x0, 0xf8, 0x0, 0x0,
    0x0, 0x7f, 0xfc, 0x0, 0xff, 0xf8, 0x1, 0xff,
    0xf0, 0x3, 0xff, 0xe0,

    /* U+003A ":" */
    0xff, 0xff, 0xff, 0xff, 0xff, 0xf8, 0x0, 0x0,
    0x0, 0x0, 0x0, 0x1, 0xff, 0xff, 0xff, 0xff,
    0xff, 0xf0
};


/*---------------------
 *  GLYPH DESCRIPTION
 *--------------------*/

static const lv_font_fmt_txt_glyph_dsc_t glyph_dsc[] = {
    {.bitmap_index = 0, .adv_w = 0, .box_w = 0, .box_h = 0, .ofs_x = 0, .ofs_y = 0} /* id = 0 reserved */,
    {.bitmap_index = 0, .adv_w = 432, .box_w = 23, .box_h = 32, .ofs_x = 0, .ofs_y = 0},
    {.bitmap_index = 92, .adv_w = 432, .box_w = 23, .box_h = 32, .ofs_x = 0, .ofs_y = 0},
    {.bitmap_index = 184, .adv_w = 432, .box_w = 23, .box_h = 32, .ofs_x = 0, .ofs_y = 0},
    {.bitmap_index = 276, .adv_w = 432, .box_w = 23, .box_h = 32, .ofs_x = 0, .ofs_y = 0},
    {.bitmap_index = 368, .adv_w = 432, .box_w = 23, .box_h = 32, .ofs_x = 0, .ofs_y = 0},
    {.bitmap_index = 460, .adv_w = 432, .box_w = 23, .box_h = 32, .ofs_x = 0, .ofs_y = 0},
    {.bitmap_index = 552, .adv_w = 432, .box_w = 23, .box_h = 32, .ofs_x = 0, .ofs_y = 0},
    {.bitmap_index = 644, .adv_w = 432, .box_w = 23, .box_h = 32, .ofs_x = 0, .ofs_y = 0},
    {.bitmap_index = 736, .adv_w = 432, .box_w = 23, .box_h = 32, .ofs_x = 0, .ofs_y = 0},
    {.bitmap_index = 828, .adv_w = 432, .box_w = 23, .box_h = 32, .ofs_x = 0, .ofs_y = 0},
    {.bitmap_index = 920, .adv_w = 432, .box_w = 5, .box_h = 28, .ofs_x = 9, .ofs_y = 0}
};

/*---------------------
 *  CHARACTER MAPPING
 *--------------------*/



/*Collect the unicode lists and glyph_id offsets*/
static const lv_font_fmt_txt_cmap_t cmaps[] =
{
    {
        .range_start = 48, .range_length = 11, .glyph_id_start = 1,
        .unicode_list = NULL, .glyph_id_ofs_list = NULL, .list_length = 0, .type = LV_FONT_FMT_TXT_CMAP_FORMAT0_TINY
    }
};



/*--------------------
 *  ALL CUSTOM DATA
 *--------------------*/

#if LVGL_VERSION_MAJOR == 8
/*Store all the custom data of the font*/
static  lv_font_fmt_txt_glyph_cache_t cache;
#endif

#if LVGL_VERSION_MAJOR >= 8
static const lv_font_fmt_txt_dsc_t font_dsc = {
#else
static lv_font_fmt_txt_dsc_t font_dsc = {
#endif
    .glyph_bitmap = glyph_bitmap,
    .glyph_dsc = glyph_dsc,
    .cmaps = cmaps,
    .kern_dsc = NULL,
    .kern_scale = 0,
    .cmap_num = 1,
    .bpp = 1,
    .kern_classes = 0,
    .bitmap_format = 0,
#if LVGL_VERSION_MAJOR == 8
    .cache = &cache
#endif

};



/*-----------------
 *  PUBLIC FONT
 *----------------*/

/*Initialize a public general font descriptor*/
#if LVGL_VERSION_MAJOR >= 8
const lv_font_t monogram_lower_numbers_72 = {
#else
lv_font_t monogram_lower_numbers_72 = {
#endif
    .get_glyph_dsc = lv_font_get_glyph_dsc_fmt_txt,    /*Function pointer to get glyph's data*/
    .get_glyph_bitmap = lv_font_get_bitmap_fmt_txt,    /*Function pointer to get glyph's bitmap*/
    .line_height = 32,          /*The maximum line height required by the font*/
    .base_line = 0,             /*Baseline measured from the bottom of the line*/
#if !(LVGL_VERSION_MAJOR == 6 && LVGL_VERSION_MINOR == 0)
    .subpx = LV_FONT_SUBPX_NONE,
#endif
#if LV_VERSION_CHECK(7, 4, 0) || LVGL_VERSION_MAJOR >= 8
    .underline_position = -9,
    .underline_thickness = 4,
#endif
    .dsc = &font_dsc,          /*The custom font data. Will be accessed by `get_glyph_bitmap/dsc` */
#if LV_VERSION_CHECK(8, 2, 0) || LVGL_VERSION_MAJOR >= 9
    .fallback = NULL,
#endif
    .user_data = NULL,
};



#endif /*#if MONOGRAM_LOWER_NUMBERS_72*/
